rattboi/vectrex-cart/docs/brett-cart-meas.png

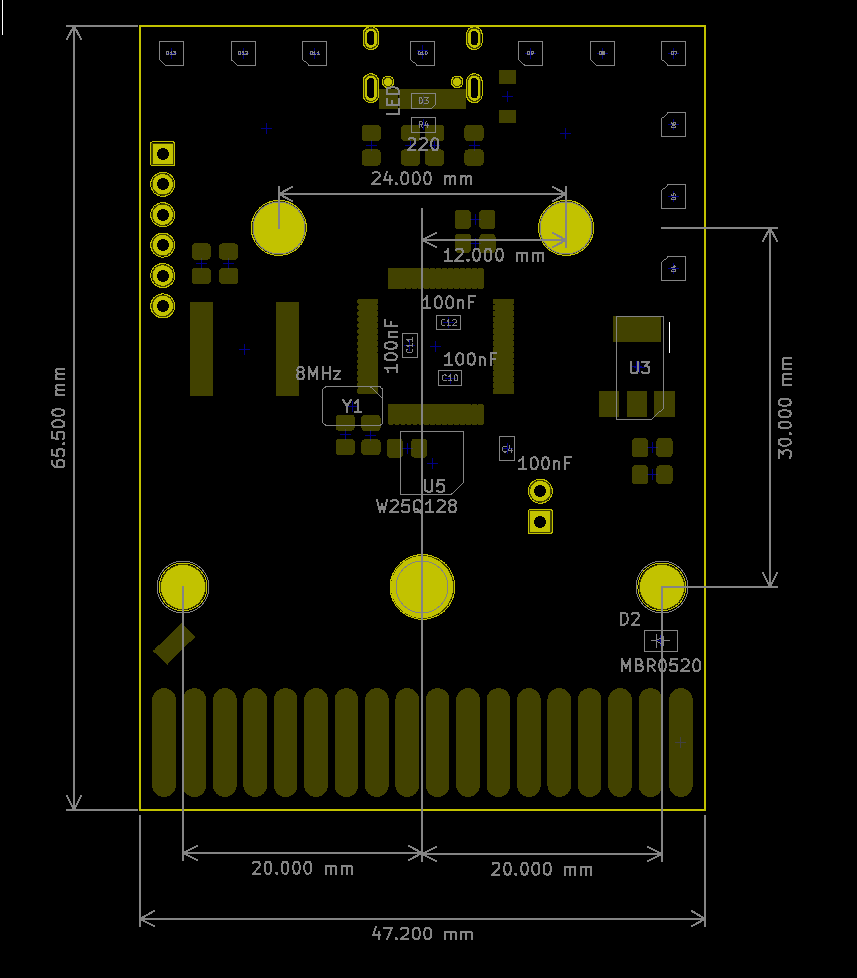
docs/brett-cart-meas.png
