rattboi/vectrex-cart/docs/tony-cart-meas.jpg

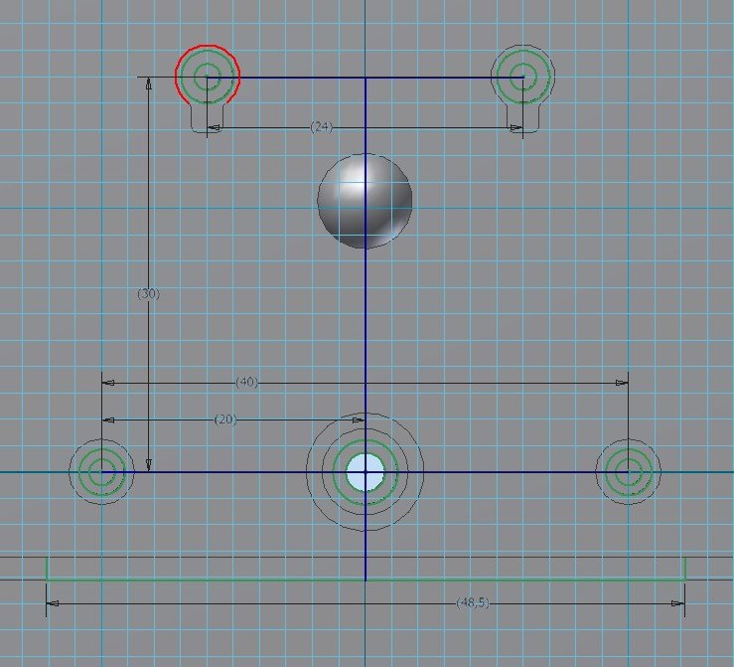
docs/tony-cart-meas.jpg
