rattboi/vectrex-cart/hall-of-fame/02 - Mike Danick - v0.1/v0.1-bot.jpg

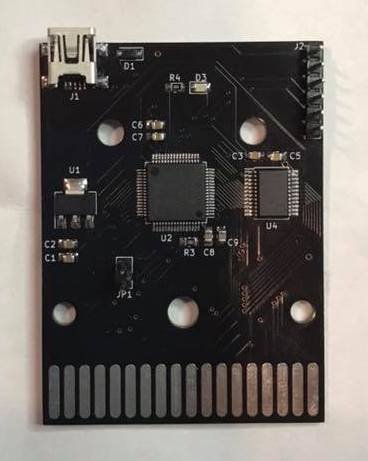
hall-of-fame/02 - Mike Danick - v0.1/v0.1-bot.jpg
