rattboi/vectrex-cart/hall-of-fame/03 - Brett Walach - v0.2/v0.2 - bot.jpg

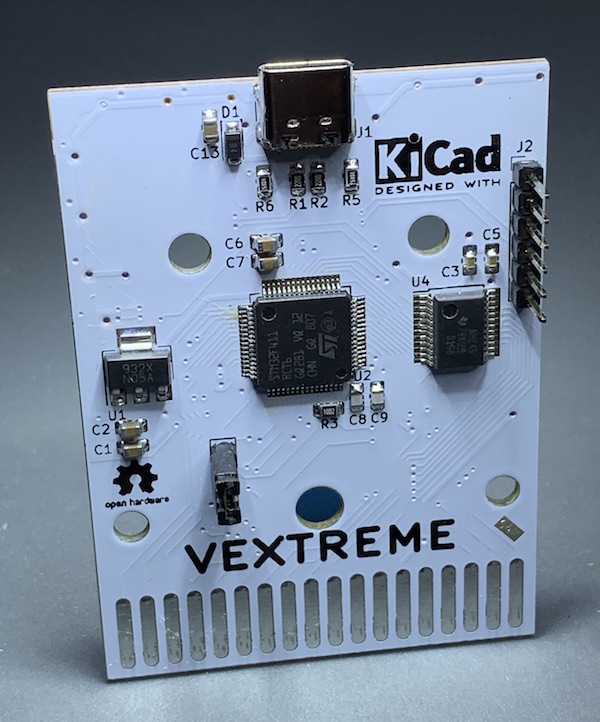
hall-of-fame/03 - Brett Walach - v0.2/v0.2 - bot.jpg
