rattboi/vectrex-cart/hall-of-fame/03 - Brett Walach - v0.2/v0.2 - top.jpg

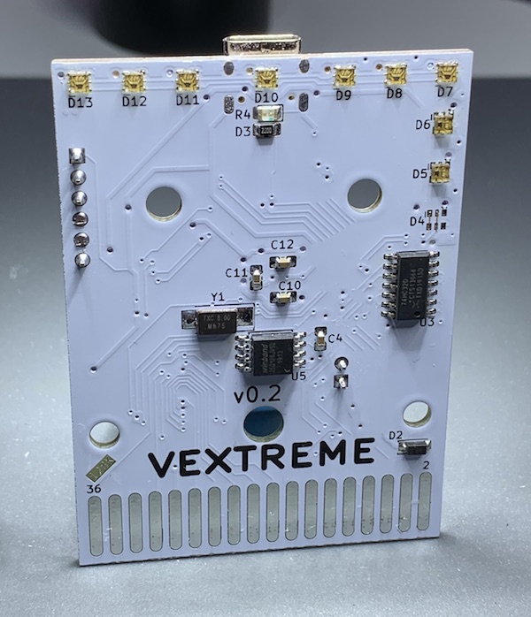
hall-of-fame/03 - Brett Walach - v0.2/v0.2 - top.jpg
