rattboi/vectrex-cart/hall-of-fame/04 - Malban - v0.2/v0.2 - bot.jpg

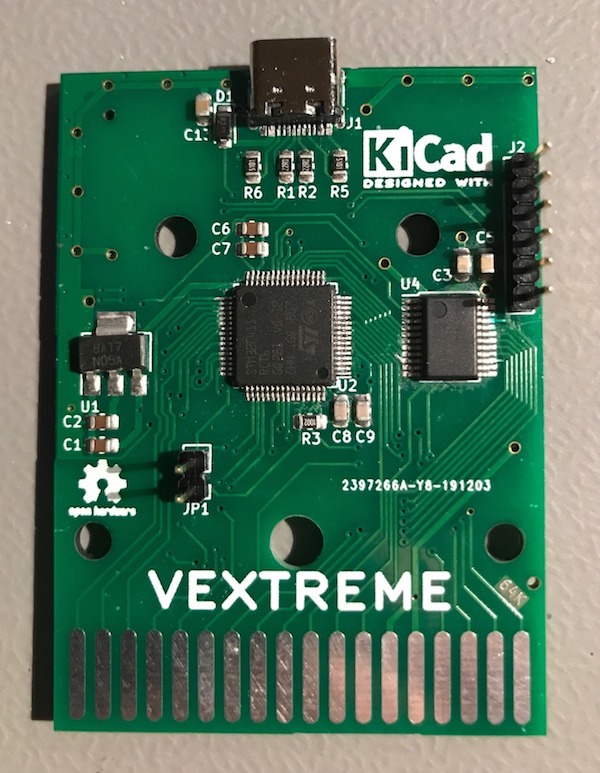
hall-of-fame/04 - Malban - v0.2/v0.2 - bot.jpg
