rattboi/vectrex-cart/hall-of-fame/04 - Malban - v0.2/v0.2 - menu.png

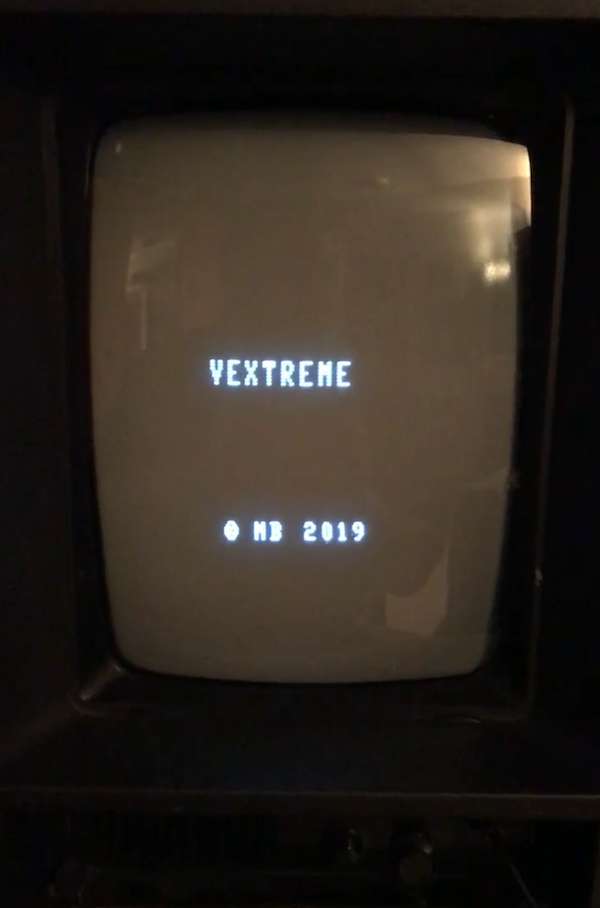
hall-of-fame/04 - Malban - v0.2/v0.2 - menu.png
