rattboi/vectrex-cart/hall-of-fame/04 - Malban - v0.2/v0.2 - top.jpg

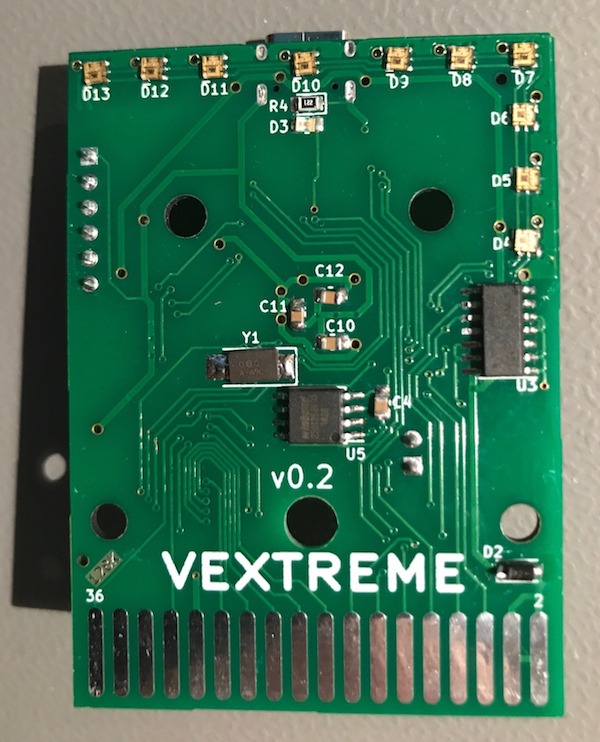
hall-of-fame/04 - Malban - v0.2/v0.2 - top.jpg
