rattboi/vectrex-cart/hall-of-fame/05 - Filippo Maggioni - v0.2/v0.2 - menu.png

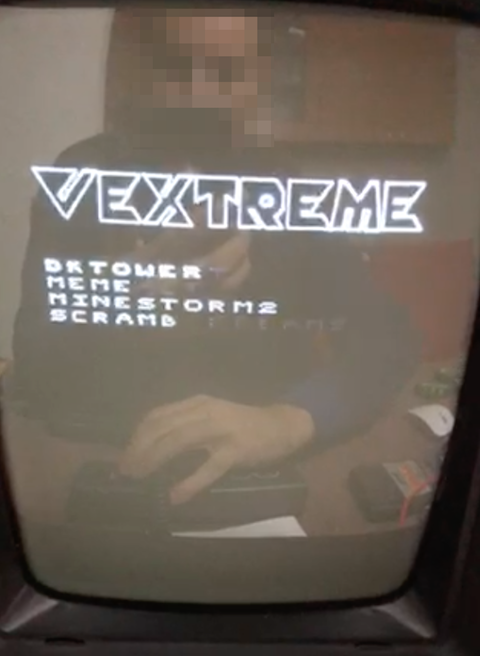
hall-of-fame/05 - Filippo Maggioni - v0.2/v0.2 - menu.png
