rattboi/vectrex-cart/hall-of-fame/05 - Filippo Maggioni - v0.2/v0.2 - top2.jpg

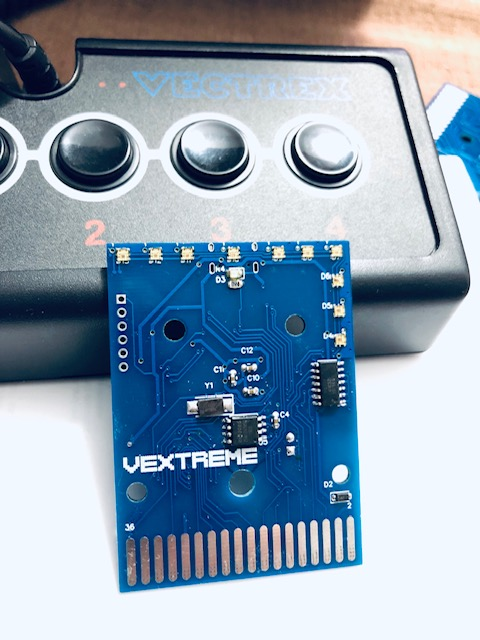
hall-of-fame/05 - Filippo Maggioni - v0.2/v0.2 - top2.jpg
