rattboi/vectrex-cart/hall-of-fame/05 - Filippo Maggioni - v0.2/v0.2 - top.jpg

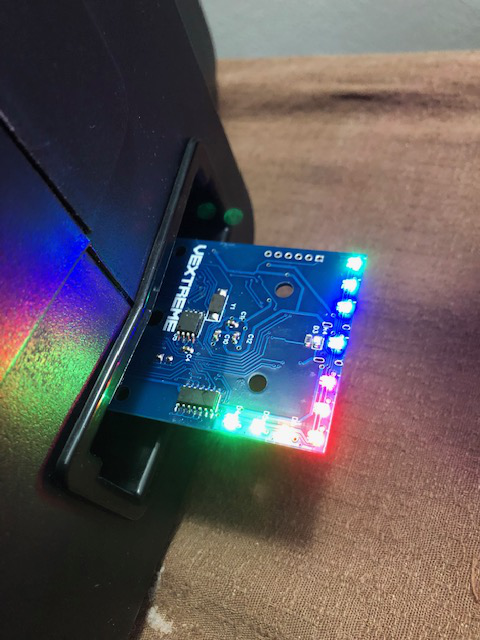
hall-of-fame/05 - Filippo Maggioni - v0.2/v0.2 - top.jpg
