rattboi/vectrex-cart/images/veccart-3d-back.png

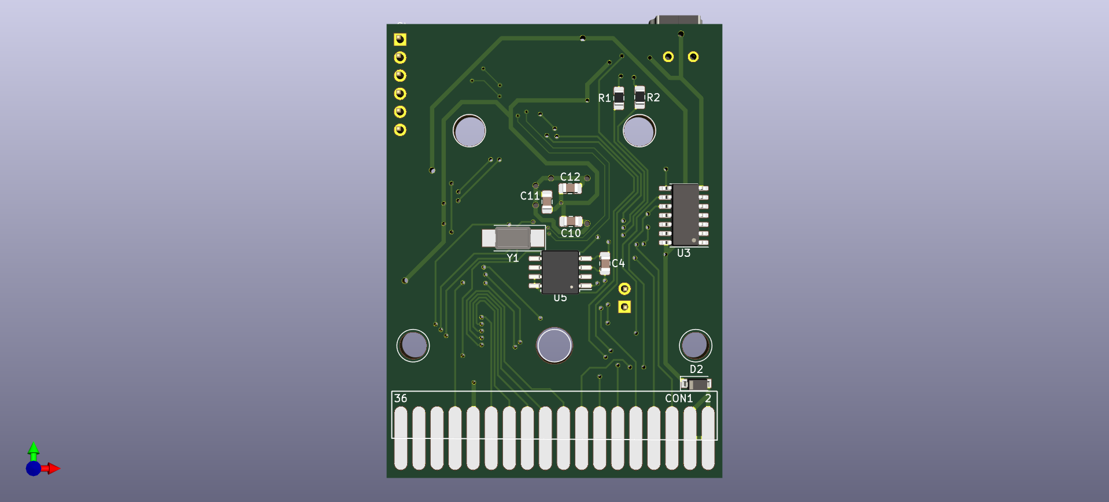
images/veccart-3d-back.png
