rattboi/vectrex-cart/images/veccart-3d-front.png

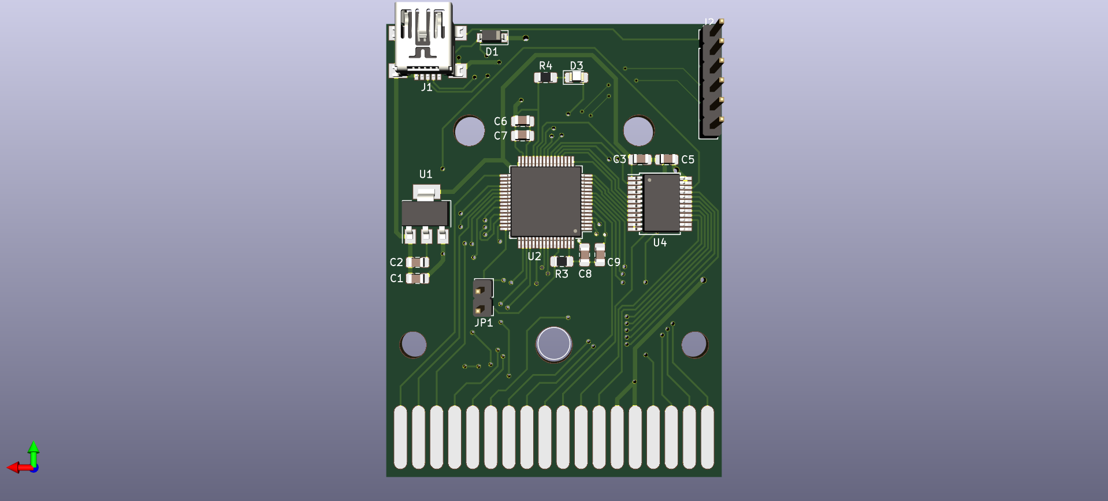
images/veccart-3d-front.png
