rattboi/vectrex-cart/code/veccart/msc.c

/*
 * This file is part of the libopencm3 project.
 *
 * Copyright (C) 2013 Weston Schmidt <weston_schmidt@alumni.purdue.edu>
 * Copyright (C) 2013 Pavol Rusnak <stick@gk2.sk>
 *
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
 * You should have received a copy of the GNU Lesser General Public License
 * along with this library.  If not, see <http://www.gnu.org/licenses/>.
 */

#include <stdlib.h>

#include <libopencm3/stm32/rcc.h>
#include <libopencm3/stm32/gpio.h>
#include <libopencm3/stm32/spi.h>
#include <libopencm3/usb/usbd.h>
#include <libopencm3/usb/msc.h>
#include <libopencm3/cm3/nvic.h>
#include <libopencm3/cm3/systick.h>
#include "flash.h"
#include "xprintf.h"
#include "delay.h"

#include "msc.h"

static const struct usb_device_descriptor dev_descr = {
	.bLength = USB_DT_DEVICE_SIZE,
	.bDescriptorType = USB_DT_DEVICE,
	.bcdUSB = 0x0110,
	.bDeviceClass = 0,
	.bDeviceSubClass = 0,
	.bDeviceProtocol = 0,
	.bMaxPacketSize0 = 64,
	.idVendor = 0x0483,
	.idProduct = 0x5741,
	.bcdDevice = 0x0200,
	.iManufacturer = 1,
	.iProduct = 2,
	.iSerialNumber = 3,
	.bNumConfigurations = 1,
};

static const struct usb_endpoint_descriptor msc_endp[] = {{
	.bLength = USB_DT_ENDPOINT_SIZE,
	.bDescriptorType = USB_DT_ENDPOINT,
	.bEndpointAddress = 0x01,
	.bmAttributes = USB_ENDPOINT_ATTR_BULK,
	.wMaxPacketSize = 64,
	.bInterval = 0,
}, {
	.bLength = USB_DT_ENDPOINT_SIZE,
	.bDescriptorType = USB_DT_ENDPOINT,
	.bEndpointAddress = 0x82,
	.bmAttributes = USB_ENDPOINT_ATTR_BULK,
	.wMaxPacketSize = 64,
	.bInterval = 0,
}};

static const struct usb_interface_descriptor msc_iface[] = {{
	.bLength = USB_DT_INTERFACE_SIZE,
	.bDescriptorType = USB_DT_INTERFACE,
	.bInterfaceNumber = 0,
	.bAlternateSetting = 0,
	.bNumEndpoints = 2,
	.bInterfaceClass = USB_CLASS_MSC,
	.bInterfaceSubClass = USB_MSC_SUBCLASS_SCSI,
	.bInterfaceProtocol = USB_MSC_PROTOCOL_BBB,
	.iInterface = 0,
	.endpoint = msc_endp,
	.extra = NULL,
	.extralen = 0
}};

static const struct usb_interface ifaces[] = {{
	.num_altsetting = 1,
	.altsetting = msc_iface,
}};

static const struct usb_config_descriptor config_descr = {
	.bLength = USB_DT_CONFIGURATION_SIZE,
	.bDescriptorType = USB_DT_CONFIGURATION,
	.wTotalLength = 0,
	.bNumInterfaces = 1,
	.bConfigurationValue = 1,
	.iConfiguration = 0,
	.bmAttributes = 0x80,
	.bMaxPower = 0x32,
	.interface = ifaces,
};

static const char *usb_strings[] = {
	"PlayVectrex.com",
	"VEXTREME",
	"0000",
};


static usbd_device *msc_dev;
/* Buffer to be used for control requests. */
static uint8_t usbd_control_buffer[128];

int ramdiskmain(void) {
//	rcc_clock_setup_hse_3v3(&hse_8mhz_3v3[CLOCK_3V3_120MHZ]);

	rcc_periph_clock_enable(RCC_GPIOA);
	rcc_periph_clock_enable(RCC_OTGFS);

	gpio_mode_setup(GPIOA, GPIO_MODE_AF, GPIO_PUPD_NONE,
			GPIO9 | GPIO11 | GPIO12);
	gpio_set_af(GPIOA, GPIO_AF10, GPIO9 | GPIO11 | GPIO12);

	flashInit();

	msc_dev = usbd_init(&otgfs_usb_driver, &dev_descr, &config_descr,
			    usb_strings, 3,
			    usbd_control_buffer, sizeof(usbd_control_buffer));

	usb_msc_init(msc_dev, 0x82, 64, 0x01, 64, "GPL3", "VEXTREME",
		"0", (16*1024*2)-16, flashReadBlk, flashWriteBlk);


	uint32_t lastFlashTick = millis();
	while(1) {
		usbd_poll(msc_dev);
		if (millis() - lastFlashTick >= 20UL) {
			lastFlashTick = millis();
			flashTick();
		}
	}
}
